drewfus0/eink_clock/include/FreeSansBold70pt7b.h

#pragma once
#include <Adafruit_GFX.h>

// Native High-Resolution TrueType Font at 1:1 Pixel Mapping (No 3x3 Block Scaling)
// Generated from FreeSansBold.ttf at 70pt (141 DPI) for ASCII 0x20 to 0x3A

const uint8_t FreeSansBold70pt7bBitmaps[] PROGMEM = {
    0xFF, 0xFF, 0xFF, 0xFF, 0xFF, 0xFF, 0xFF, 0xFF, 0xFF, 0xFF, 0xFF, 0xFF,
    0xFF, 0xFF, 0xFF, 0xFF, 0xFF, 0xFF, 0xFF, 0xFF, 0xFF, 0xFF, 0xFF, 0xFF,
    0xFF, 0xFF, 0xFF, 0xFF, 0xFF, 0xFF, 0xFF, 0xFF, 0xFF, 0xFF, 0xFF, 0xFF,
    0xFF, 0xFF, 0xFF, 0xFF, 0xFF, 0xFF, 0xFF, 0xFF, 0xFF, 0xFF, 0xFF, 0xFF,
    0xFF, 0xFF, 0xFF, 0xFF, 0xFF, 0xFF, 0xFF, 0xFF, 0xFF, 0xFF, 0xFF, 0xFF,
    0xFF, 0xFF, 0xFF, 0xFF, 0xFF, 0xFF, 0xFF, 0xFF, 0xFF, 0xFF, 0xFF, 0xFF,
    0xFF, 0xFF, 0xFF, 0xFF, 0xFF, 0xFF, 0xFF, 0xFF, 0xFF, 0xFF, 0xFF, 0xFF,
    0x7F, 0xFF, 0xF3, 0xFF, 0xFF, 0x9F, 0xFF, 0xFC, 0xFF, 0xFF, 0xE7, 0xFF,
    0xFF, 0x3F, 0xFF, 0xF9, 0xFF, 0xFF, 0xCF, 0xFF, 0xFC, 0x3F, 0xFF, 0xE1,
    0xFF, 0xFF, 0x0F, 0xFF, 0xF8, 0x7F, 0xFF, 0xC3, 0xFF, 0xFE, 0x1F, 0xFF,
    0xF0, 0xFF, 0xFF, 0x83, 0xFF, 0xF8, 0x1F, 0xFF, 0xC0, 0xFF, 0xFE, 0x07,
    0xFF, 0xF0, 0x3F, 0xFF, 0x81, 0xFF, 0xFC, 0x0F, 0xFF, 0xE0, 0x3F, 0xFE,
    0x01, 0xFF, 0xF0, 0x0F, 0xFF, 0x80, 0x7F, 0xFC, 0x03, 0xFF, 0xE0, 0x1F,
    0xFF, 0x00, 0xFF, 0xF8, 0x07, 0xFF, 0x80, 0x1F, 0xFC, 0x00, 0xFF, 0xE0,
    0x07, 0xFF, 0x00, 0x3F, 0xF8, 0x01, 0xFF, 0xC0, 0x0F, 0xFE, 0x00, 0x7F,
    0xE0, 0x01, 0xFF, 0x00, 0x0F, 0xF8, 0x00, 0x00, 0x00, 0x00, 0x00, 0x00,
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
    { 14989,  66, 102,  76,   4,  -98 }, // 0x39 '9'
    { 15831,  21,  71,  34,   7,  -70 } // 0x3A ':'
};

const GFXfont FreeSansBold70pt7b PROGMEM = {
    (uint8_t *)FreeSansBold70pt7bBitmaps,
    (GFXglyph *)FreeSansBold70pt7bGlyphs,
    0x20, 0x3A, 158
};
